LKbrilliant/ATMOS/imgs/img_01.jpg

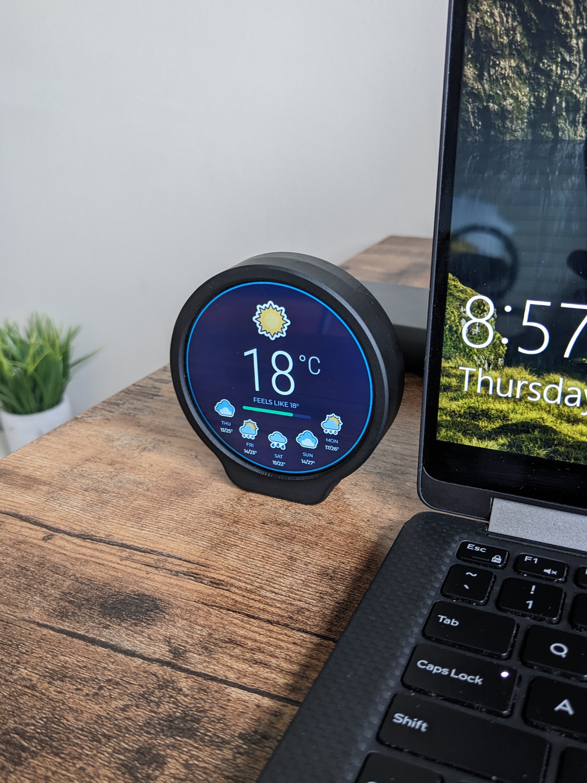
imgs/img_01.jpg
