LKbrilliant/ATMOS/src/atmos/components/esp-idf-wifi-provisioner/docs/example.png

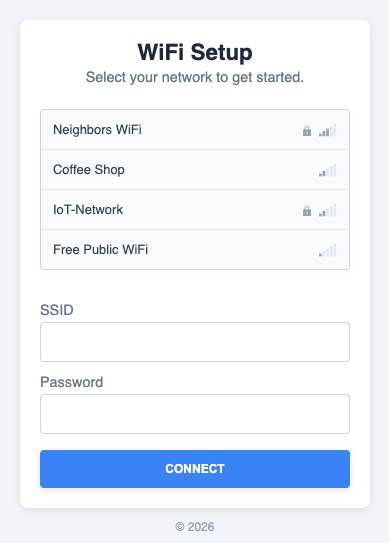
src/atmos/components/esp-idf-wifi-provisioner/docs/example.png
