LKbrilliant/ATMOS/src/atmos/main/roboto_condensed_light_12.c

/*******************************************************************************
 * Size: 12 px
 * Bpp: 4
 * Opts: --bpp 4 --size 12 --no-compress --stride 1 --align 1 --font RobotoCondensed-Light.ttf --symbols °/ --range 32-127 --format lvgl -o roboto_condensed_light_12.c
 ******************************************************************************/

#ifdef __has_include
    #if __has_include("lvgl.h")
        #ifndef LV_LVGL_H_INCLUDE_SIMPLE
            #define LV_LVGL_H_INCLUDE_SIMPLE
        #endif
    #endif
#endif

#ifdef LV_LVGL_H_INCLUDE_SIMPLE
    #include "lvgl.h"
#else
    #include "lvgl/lvgl.h"
#endif



#ifndef ROBOTO_CONDENSED_LIGHT_12
#define ROBOTO_CONDENSED_LIGHT_12 1
#endif

#if ROBOTO_CONDENSED_LIGHT_12

/*-----------------
 *    BITMAPS
 *----------------*/

/*Store the image of the glyphs*/
static LV_ATTRIBUTE_LARGE_CONST const uint8_t glyph_bitmap[] = {
    /* U+0020 " " */

    /* U+0021 "!" */
    0x1a, 0x9, 0x9, 0x9, 0x9, 0x9, 0x6, 0x0,
    0xa,

    /* U+0022 "\"" */
    0x27, 0x92, 0x68, 0x24, 0x70,

    /* U+0023 "#" */
    0x0, 0x43, 0x44, 0x0, 0x6, 0x16, 0x10, 0x9,
    0xd9, 0xd9, 0x0, 0x8, 0x8, 0x0, 0x0, 0x80,
    0x80, 0x0, 0x7, 0x8, 0x0, 0x4a, 0xba, 0xc6,
    0x0, 0x52, 0x53, 0x0, 0x7, 0x7, 0x0, 0x0,

    /* U+0024 "$" */
    0x0, 0x35, 0x0, 0x0, 0x35, 0x0, 0x5, 0xbc,
    0x50, 0xb, 0x0, 0xb0, 0xa, 0x0, 0x61, 0xa,
    0x20, 0x0, 0x1, 0x9a, 0x10, 0x0, 0x2, 0xb0,
    0x33, 0x0, 0x82, 0x29, 0x0, 0xb0, 0x7, 0xbc,
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
    0x7, 0xb0,

    /* U+0075 "u" */
    0x28, 0x0, 0xa2, 0x80, 0xa, 0x28, 0x0, 0xa2,
    0x80, 0xa, 0x28, 0x0, 0xa0, 0xa0, 0xc, 0x8,
    0xba, 0xb0,

    /* U+0076 "v" */
    0x81, 0x0, 0x94, 0x60, 0x45, 0x9, 0x8, 0x10,
    0x90, 0x90, 0x6, 0x48, 0x0, 0x2c, 0x30, 0x0,
    0xc0, 0x0,

    /* U+0077 "w" */
    0x72, 0x8, 0x40, 0x64, 0x46, 0xa, 0x80, 0x91,
    0x9, 0x9, 0x90, 0xa0, 0xa, 0x35, 0x81, 0x90,
    0x9, 0x81, 0x57, 0x60, 0x6, 0xc0, 0x1d, 0x20,
    0x2, 0xa0, 0xc, 0x0,

    /* U+0078 "x" */
    0x56, 0x4, 0x70, 0xa0, 0xa0, 0x4, 0xa6, 0x0,
    0xe, 0x10, 0x5, 0x87, 0x0, 0xb0, 0xa1, 0x65,
    0x3, 0x80,

    /* U+0079 "y" */
    0x91, 0x1, 0x95, 0x60, 0x55, 0x9, 0x9, 0x10,
    0xa0, 0xa0, 0x7, 0x48, 0x0, 0x3c, 0x40, 0x0,
    0xe0, 0x0, 0x9, 0x0, 0x2, 0x70, 0x4, 0xb1,
    0x0,

    /* U+007A "z" */
    0x3a, 0xac, 0x70, 0x0, 0xa1, 0x0, 0x47, 0x0,
    0xb, 0x0, 0x6, 0x50, 0x0, 0xa0, 0x0, 0x6d,
    0xaa, 0x80,

    /* U+007B "{" */
    0x0, 0x63, 0x2, 0x80, 0x6, 0x40, 0x6, 0x30,
    0x6, 0x30, 0x9, 0x10, 0x59, 0x0, 0x8, 0x10,
    0x6, 0x30, 0x6, 0x30, 0x5, 0x40, 0x1, 0x90,
    0x0, 0x43,

    /* U+007C "|" */
    0x99, 0x99, 0x99, 0x99, 0x99, 0x90,

    /* U+007D "}" */
    0x72, 0x0, 0xa, 0x0, 0xa, 0x0, 0xa, 0x0,
    0xa, 0x0, 0x7, 0x30, 0x1, 0xd2, 0x7, 0x30,
    0xa, 0x0, 0xa, 0x0, 0xa, 0x0, 0xa, 0x0,
    0x72, 0x0,

    /* U+007E "~" */
    0x6, 0xb3, 0x3, 0x30, 0x90, 0xa1, 0x72, 0x14,
    0x1, 0xa7, 0x0,

    /* U+00B0 "°" */
    0x6, 0x92, 0x17, 0x8, 0x17, 0x8, 0x6, 0x92
};


/*---------------------
 *  GLYPH DESCRIPTION
 *--------------------*/

static const lv_font_fmt_txt_glyph_dsc_t glyph_dsc[] = {
    {.bitmap_index = 0, .adv_w = 0, .box_w = 0, .box_h = 0, .ofs_x = 0, .ofs_y = 0} /* id = 0 reserved */,
    {.bitmap_index = 0, .adv_w = 43, .box_w = 0, .box_h = 0, .ofs_x = 0, .ofs_y = 0},
    {.bitmap_index = 0, .adv_w = 41, .box_w = 2, .box_h = 9, .ofs_x = 0, .ofs_y = 0},
    {.bitmap_index = 9, .adv_w = 55, .box_w = 3, .box_h = 3, .ofs_x = 0, .ofs_y = 7},
    {.bitmap_index = 14, .adv_w = 99, .box_w = 7, .box_h = 9, .ofs_x = 0, .ofs_y = 0},
    {.bitmap_index = 46, .adv_w = 93, .box_w = 6, .box_h = 13, .ofs_x = 0, .ofs_y = -2},
    {.bitmap_index = 85, .adv_w = 123, .box_w = 8, .box_h = 9, .ofs_x = 0, .ofs_y = 0},
    {.bitmap_index = 121, .adv_w = 103, .box_w = 7, .box_h = 9, .ofs_x = 0, .ofs_y = 0},
    {.bitmap_index = 153, .adv_w = 33, .box_w = 2, .box_h = 3, .ofs_x = 0, .ofs_y = 7},
    {.bitmap_index = 156, .adv_w = 56, .box_w = 4, .box_h = 14, .ofs_x = 0, .ofs_y = -3},
    {.bitmap_index = 184, .adv_w = 57, .box_w = 3, .box_h = 14, .ofs_x = 0, .ofs_y = -3},
    {.bitmap_index = 205, .adv_w = 81, .box_w = 5, .box_h = 6, .ofs_x = 0, .ofs_y = 3},
    {.bitmap_index = 220, .adv_w = 95, .box_w = 6, .box_h = 7, .ofs_x = 0, .ofs_y = 1},
    {.bitmap_index = 241, .adv_w = 37, .box_w = 2, .box_h = 3, .ofs_x = 0, .ofs_y = -2},
    {.bitmap_index = 244, .adv_w = 50, .box_w = 3, .box_h = 1, .ofs_x = 0, .ofs_y = 4},
    {.bitmap_index = 246, .adv_w = 46, .box_w = 2, .box_h = 2, .ofs_x = 0, .ofs_y = 0},
    {.bitmap_index = 248, .adv_w = 68, .box_w = 4, .box_h = 10, .ofs_x = 0, .ofs_y = -1},
    {.bitmap_index = 268, .adv_w = 93, .box_w = 6, .box_h = 9, .ofs_x = 0, .ofs_y = 0},
    {.bitmap_index = 295, .adv_w = 93, .box_w = 4, .box_h = 10, .ofs_x = 0, .ofs_y = 0},
    {.bitmap_index = 315, .adv_w = 93, .box_w = 6, .box_h = 9, .ofs_x = 0, .ofs_y = 0},
    {.bitmap_index = 342, .adv_w = 93, .box_w = 6, .box_h = 9, .ofs_x = 0, .ofs_y = 0},
    {.bitmap_index = 369, .adv_w = 93, .box_w = 6, .box_h = 9, .ofs_x = 0, .ofs_y = 0},
    {.bitmap_index = 396, .adv_w = 93, .box_w = 6, .box_h = 9, .ofs_x = 0, .ofs_y = 0},
    {.bitmap_index = 423, .adv_w = 93, .box_w = 6, .box_h = 9, .ofs_x = 0, .ofs_y = 0},
    {.bitmap_index = 450, .adv_w = 93, .box_w = 6, .box_h = 9, .ofs_x = 0, .ofs_y = 0},
    {.bitmap_index = 477, .adv_w = 93, .box_w = 6, .box_h = 9, .ofs_x = 0, .ofs_y = 0},
    {.bitmap_index = 504, .adv_w = 93, .box_w = 6, .box_h = 9, .ofs_x = 0, .ofs_y = 0},
    {.bitmap_index = 531, .adv_w = 39, .box_w = 2, .box_h = 7, .ofs_x = 0, .ofs_y = 0},
    {.bitmap_index = 538, .adv_w = 36, .box_w = 2, .box_h = 9, .ofs_x = 0, .ofs_y = -2},
    {.bitmap_index = 547, .adv_w = 86, .box_w = 5, .box_h = 6, .ofs_x = 0, .ofs_y = 1},
    {.bitmap_index = 562, .adv_w = 93, .box_w = 5, .box_h = 4, .ofs_x = 0, .ofs_y = 3},
    {.bitmap_index = 572, .adv_w = 88, .box_w = 5, .box_h = 6, .ofs_x = 0, .ofs_y = 1},
    {.bitmap_index = 587, .adv_w = 78, .box_w = 5, .box_h = 9, .ofs_x = 0, .ofs_y = 0},
    {.bitmap_index = 610, .adv_w = 151, .box_w = 9, .box_h = 12, .ofs_x = 0, .ofs_y = -3},
    {.bitmap_index = 664, .adv_w = 105, .box_w = 7, .box_h = 9, .ofs_x = 0, .ofs_y = 0},
    {.bitmap_index = 696, .adv_w = 103, .box_w = 5, .box_h = 9, .ofs_x = 1, .ofs_y = 0},
    {.bitmap_index = 719, .adv_w = 109, .box_w = 7, .box_h = 9, .ofs_x = 0, .ofs_y = 0},
    {.bitmap_index = 751, .adv_w = 109, .box_w = 6, .box_h = 9, .ofs_x = 1, .ofs_y = 0},
    {.bitmap_index = 778, .adv_w = 96, .box_w = 5, .box_h = 9, .ofs_x = 1, .ofs_y = 0},
    {.bitmap_index = 801, .adv_w = 94, .box_w = 5, .box_h = 9, .ofs_x = 1, .ofs_y = 0},
    {.bitmap_index = 824, .adv_w = 114, .box_w = 7, .box_h = 9, .ofs_x = 0, .ofs_y = 0},
    {.bitmap_index = 856, .adv_w = 118, .box_w = 6, .box_h = 9, .ofs_x = 1, .ofs_y = 0},
    {.bitmap_index = 883, .adv_w = 47, .box_w = 1, .box_h = 9, .ofs_x = 1, .ofs_y = 0},
    {.bitmap_index = 888, .adv_w = 93, .box_w = 5, .box_h = 9, .ofs_x = 0, .ofs_y = 0},
    {.bitmap_index = 911, .adv_w = 105, .box_w = 6, .box_h = 9, .ofs_x = 1, .ofs_y = 0},
    {.bitmap_index = 938, .adv_w = 89, .box_w = 5, .box_h = 9, .ofs_x = 1, .ofs_y = 0},
    {.bitmap_index = 961, .adv_w = 144, .box_w = 7, .box_h = 9, .ofs_x = 1, .ofs_y = 0},
    {.bitmap_index = 993, .adv_w = 118, .box_w = 6, .box_h = 9, .ofs_x = 1, .ofs_y = 0},
    {.bitmap_index = 1020, .adv_w = 113, .box_w = 7, .box_h = 9, .ofs_x = 0, .ofs_y = 0},
    {.bitmap_index = 1052, .adv_w = 104, .box_w = 5, .box_h = 9, .ofs_x = 1, .ofs_y = 0},
    {.bitmap_index = 1075, .adv_w = 113, .box_w = 7, .box_h = 11, .ofs_x = 0, .ofs_y = -2},
    {.bitmap_index = 1114, .adv_w = 106, .box_w = 6, .box_h = 9, .ofs_x = 1, .ofs_y = 0},
    {.bitmap_index = 1141, .adv_w = 99, .box_w = 6, .box_h = 9, .ofs_x = 0, .ofs_y = 0},
    {.bitmap_index = 1168, .adv_w = 100, .box_w = 6, .box_h = 9, .ofs_x = 0, .ofs_y = 0},
    {.bitmap_index = 1195, .adv_w = 110, .box_w = 6, .box_h = 9, .ofs_x = 0, .ofs_y = 0},
    {.bitmap_index = 1222, .adv_w = 104, .box_w = 7, .box_h = 9, .ofs_x = 0, .ofs_y = 0},
    {.bitmap_index = 1254, .adv_w = 148, .box_w = 9, .box_h = 9, .ofs_x = 0, .ofs_y = 0},
    {.bitmap_index = 1295, .adv_w = 103, .box_w = 7, .box_h = 9, .ofs_x = 0, .ofs_y = 0},
    {.bitmap_index = 1327, .adv_w = 100, .box_w = 7, .box_h = 9, .ofs_x = 0, .ofs_y = 0},
    {.bitmap_index = 1359, .adv_w = 100, .box_w = 6, .box_h = 9, .ofs_x = 0, .ofs_y = 0},
    {.bitmap_index = 1386, .adv_w = 43, .box_w = 3, .box_h = 13, .ofs_x = 0, .ofs_y = -2},
    {.bitmap_index = 1406, .adv_w = 68, .box_w = 4, .box_h = 10, .ofs_x = 0, .ofs_y = -1},
    {.bitmap_index = 1426, .adv_w = 43, .box_w = 2, .box_h = 13, .ofs_x = 0, .ofs_y = -2},
    {.bitmap_index = 1439, .adv_w = 71, .box_w = 4, .box_h = 5, .ofs_x = 0, .ofs_y = 5},
    {.bitmap_index = 1449, .adv_w = 74, .box_w = 5, .box_h = 1, .ofs_x = 0, .ofs_y = -1},
    {.bitmap_index = 1452, .adv_w = 55, .box_w = 3, .box_h = 2, .ofs_x = 0, .ofs_y = 8},
    {.bitmap_index = 1455, .adv_w = 90, .box_w = 5, .box_h = 7, .ofs_x = 0, .ofs_y = 0},
    {.bitmap_index = 1473, .adv_w = 93, .box_w = 6, .box_h = 10, .ofs_x = 0, .ofs_y = 0},
    {.bitmap_index = 1503, .adv_w = 87, .box_w = 5, .box_h = 7, .ofs_x = 0, .ofs_y = 0},
    {.bitmap_index = 1521, .adv_w = 94, .box_w = 5, .box_h = 10, .ofs_x = 0, .ofs_y = 0},
    {.bitmap_index = 1546, .adv_w = 88, .box_w = 5, .box_h = 7, .ofs_x = 0, .ofs_y = 0},
    {.bitmap_index = 1564, .adv_w = 58, .box_w = 4, .box_h = 10, .ofs_x = 0, .ofs_y = 0},
    {.bitmap_index = 1584, .adv_w = 93, .box_w = 5, .box_h = 10, .ofs_x = 0, .ofs_y = -3},
    {.bitmap_index = 1609, .adv_w = 92, .box_w = 5, .box_h = 10, .ofs_x = 0, .ofs_y = 0},
    {.bitmap_index = 1634, .adv_w = 41, .box_w = 2, .box_h = 9, .ofs_x = 0, .ofs_y = 0},
    {.bitmap_index = 1643, .adv_w = 41, .box_w = 3, .box_h = 12, .ofs_x = -1, .ofs_y = -3},
    {.bitmap_index = 1661, .adv_w = 83, .box_w = 6, .box_h = 10, .ofs_x = 0, .ofs_y = 0},
    {.bitmap_index = 1691, .adv_w = 41, .box_w = 2, .box_h = 10, .ofs_x = 0, .ofs_y = 0},
    {.bitmap_index = 1701, .adv_w = 146, .box_w = 9, .box_h = 7, .ofs_x = 0, .ofs_y = 0},
    {.bitmap_index = 1733, .adv_w = 93, .box_w = 5, .box_h = 7, .ofs_x = 0, .ofs_y = 0},
    {.bitmap_index = 1751, .adv_w = 94, .box_w = 6, .box_h = 7, .ofs_x = 0, .ofs_y = 0},
    {.bitmap_index = 1772, .adv_w = 93, .box_w = 6, .box_h = 10, .ofs_x = 0, .ofs_y = -3},
    {.bitmap_index = 1802, .adv_w = 94, .box_w = 5, .box_h = 10, .ofs_x = 0, .ofs_y = -3},
    {.bitmap_index = 1827, .adv_w = 58, .box_w = 4, .box_h = 7, .ofs_x = 0, .ofs_y = 0},
    {.bitmap_index = 1841, .adv_w = 86, .box_w = 5, .box_h = 7, .ofs_x = 0, .ofs_y = 0},
    {.bitmap_index = 1859, .adv_w = 56, .box_w = 4, .box_h = 9, .ofs_x = 0, .ofs_y = 0},
    {.bitmap_index = 1877, .adv_w = 92, .box_w = 5, .box_h = 7, .ofs_x = 0, .ofs_y = 0},
    {.bitmap_index = 1895, .adv_w = 81, .box_w = 5, .box_h = 7, .ofs_x = 0, .ofs_y = 0},
    {.bitmap_index = 1913, .adv_w = 125, .box_w = 8, .box_h = 7, .ofs_x = 0, .ofs_y = 0},
    {.bitmap_index = 1941, .adv_w = 83, .box_w = 5, .box_h = 7, .ofs_x = 0, .ofs_y = 0},
    {.bitmap_index = 1959, .adv_w = 80, .box_w = 5, .box_h = 10, .ofs_x = 0, .ofs_y = -3},
    {.bitmap_index = 1984, .adv_w = 83, .box_w = 5, .box_h = 7, .ofs_x = 0, .ofs_y = 0},
    {.bitmap_index = 2002, .adv_w = 57, .box_w = 4, .box_h = 13, .ofs_x = 0, .ofs_y = -3},
    {.bitmap_index = 2028, .adv_w = 43, .box_w = 1, .box_h = 11, .ofs_x = 1, .ofs_y = -2},
    {.bitmap_index = 2034, .adv_w = 57, .box_w = 4, .box_h = 13, .ofs_x = 0, .ofs_y = -3},
    {.bitmap_index = 2060, .adv_w = 114, .box_w = 7, .box_h = 3, .ofs_x = 0, .ofs_y = 3},
    {.bitmap_index = 2071, .adv_w = 73, .box_w = 4, .box_h = 4, .ofs_x = 0, .ofs_y = 6}
};

/*---------------------
 *  CHARACTER MAPPING
 *--------------------*/



/*Collect the unicode lists and glyph_id offsets*/
static const lv_font_fmt_txt_cmap_t cmaps[] =
{
    {
        .range_start = 32, .range_length = 95, .glyph_id_start = 1,
        .unicode_list = NULL, .glyph_id_ofs_list = NULL, .list_length = 0, .type = LV_FONT_FMT_TXT_CMAP_FORMAT0_TINY
    },
    {
        .range_start = 176, .range_length = 1, .glyph_id_start = 96,
        .unicode_list = NULL, .glyph_id_ofs_list = NULL, .list_length = 0, .type = LV_FONT_FMT_TXT_CMAP_FORMAT0_TINY
    }
};

/*-----------------
 *    KERNING
 *----------------*/


/*Pair left and right glyphs for kerning*/
static const uint8_t kern_pair_glyph_ids[] =
{
    3, 3,
    3, 8,
    8, 3,
    8, 8,
    13, 3,
    13, 8,
    15, 3,
    15, 8,
    16, 16
};

/* Kerning between the respective left and right glyphs
 * 4.4 format which needs to scaled with `kern_scale`*/
static const int8_t kern_pair_values[] =
{
    -10, -10, -10, -10, -16, -16, -16, -16,
    -21
};

/*Collect the kern pair's data in one place*/
static const lv_font_fmt_txt_kern_pair_t kern_pairs =
{
    .glyph_ids = kern_pair_glyph_ids,
    .values = kern_pair_values,
    .pair_cnt = 9,
    .glyph_ids_size = 0
};

/*--------------------
 *  ALL CUSTOM DATA
 *--------------------*/

#if LVGL_VERSION_MAJOR == 8
/*Store all the custom data of the font*/
static  lv_font_fmt_txt_glyph_cache_t cache;
#endif

#if LVGL_VERSION_MAJOR >= 8
static const lv_font_fmt_txt_dsc_t font_dsc = {
#else
static lv_font_fmt_txt_dsc_t font_dsc = {
#endif
    .glyph_bitmap = glyph_bitmap,
    .glyph_dsc = glyph_dsc,
    .cmaps = cmaps,
    .kern_dsc = &kern_pairs,
    .kern_scale = 16,
    .cmap_num = 2,
    .bpp = 4,
    .kern_classes = 0,
    .bitmap_format = 0,
#if LVGL_VERSION_MAJOR == 8
    .cache = &cache
#endif

};



/*-----------------
 *  PUBLIC FONT
 *----------------*/

/*Initialize a public general font descriptor*/
#if LVGL_VERSION_MAJOR >= 8
const lv_font_t roboto_condensed_light_12 = {
#else
lv_font_t roboto_condensed_light_12 = {
#endif
    .get_glyph_dsc = lv_font_get_glyph_dsc_fmt_txt,    /*Function pointer to get glyph's data*/
    .get_glyph_bitmap = lv_font_get_bitmap_fmt_txt,    /*Function pointer to get glyph's bitmap*/
    .line_height = 14,          /*The maximum line height required by the font*/
    .base_line = 3,             /*Baseline measured from the bottom of the line*/
#if !(LVGL_VERSION_MAJOR == 6 && LVGL_VERSION_MINOR == 0)
    .subpx = LV_FONT_SUBPX_NONE,
#endif
#if LV_VERSION_CHECK(7, 4, 0) || LVGL_VERSION_MAJOR >= 8
    .underline_position = -1,
    .underline_thickness = 1,
#endif
    // .static_bitmap = 0,
    .dsc = &font_dsc,          /*The custom font data. Will be accessed by `get_glyph_bitmap/dsc` */
#if LV_VERSION_CHECK(8, 2, 0) || LVGL_VERSION_MAJOR >= 9
    .fallback = NULL,
#endif
    .user_data = NULL,
};



#endif /*#if ROBOTO_CONDENSED_LIGHT_12*/
